takjn/GRRNble/GRRNble/allFonts.h

/*
 * allFonts.h font header for GLCD library 
 * The fonts listed below will be available in a sketch if this file is included
 *
 * If you create your own fonts you can add the header to this file
 *
 * Note that the build environment only holds a font in Flash if its selected 
 * so there is no penalty to including a font file here if its not used 
 */

#ifndef _allFonts_h_
#define _allFonts_h_

#ifdef __AVR__
#include <avr/pgmspace.h>
/** declare a font for AVR. */
#define GLCDFONTDECL(_n) static const uint8_t __attribute__ ((progmem))_n[]
#define readFontByte(addr) pgm_read_byte(addr)
#else  // __AVR__
/** declare a font. */
#define GLCDFONTDECL(_n) static const uint8_t _n[]
/** Fake read from flash. */
#define readFontByte(addr) (*(const unsigned char *)(addr))
#endif  // __AVR__
//------------------------------------------------------------------------------
// Font Indices
#define FONT_LENGTH			  0
#define FONT_FIXED_WIDTH	2
#define FONT_HEIGHT			  3
#define FONT_FIRST_CHAR		4
#define FONT_CHAR_COUNT		5
#define FONT_WIDTH_TABLE	6
//
// FONT_LENGTH is a 16 bit Big Endian length field.
// Unfortunately, FontCreator2 screwed up the value it put in the field
// so it is pretty much meaningless. However it still is used to indicate
// some special things.
// 00 00 (fixed width font with 1 padding pixel on right and below)
// 00 01 (fixed width font with no padding pixels)

// any other value means variable width font in FontCreator2 (thiele)
// format with pixel padding

//#include "Adafruit5x7.h"        // Font from Adafruit GFX library
//#include "font5x7.h"
//#include "lcd5x7.h"
//#include "Stang5x7.h"
//#include "X11fixed7x14.h"
//#include "X11fixed7x14B.h"
//#include "ZevvPeep8x16.h"
//
//#include "System5x7.h" 	        // system font (fixed width)
//#include "SystemFont5x7.h"      // backward compability System5x7 header
//#include "Iain5x7.h"		        // similar to system5x7 but proportional
//#include "Arial14.h"            // proportional font
//#include "Arial_bold_14.h"      // Bold proportional font
//#include "Corsiva_12.h"
//#include "Verdana_digits_24.h"  // large proportional font contains [0-9] and :
//
//#include "Callibri10.h"
//#include "Callibri11.h"
//#include "Callibri11_bold.h"
//#include "Callibri11_italic.h"
//#include "Callibri14.h"
//#include "Callibri15.h"
//#include "Cooper19.h"
//#include "Cooper21.h"
//#include "Cooper26.h"
//#include "TimesNewRoman13.h"
//#include "TimesNewRoman13_italic.h"
//#include "TimesNewRoman16.h"
//#include "TimesNewRoman16_bold.h"
//#include "TimesNewRoman16_italic.h"
//#include "Verdana12.h"
//#include "Verdana12_bold.h"
//#include "Verdana12_italic.h"
//#include "Roosewood22.h"
//#include "Roosewood26.h"
//
//#include "fixednums7x15.h"       // fixed width font - + , - . / [0-9] and :
//#include "fixednums8x16.h"       // fixed width font - + , - . / [0-9] and :
//#include "fixednums15x31.h"      // fixed width font - + , - . / [0-9] and :
//
//#include "CalBlk36.h"
//#include "CalLite24.h"
//#include "lcdnums12x16.h"	// font that looks like LCD digits
//#include "lcdnums14x24.h"	// font that looks like LCD digits
//#include "fixed_bold10x15.h"
//#include "Wendy3x5.h"
//#include "newbasic3x5.h"
//#include "TomThumbs3x6.h"
//
///*
// * These fonts require no-pad rendering code
// */
//#include "font8x8.h"		// fixed wider font but similar to system5x7 font
//#include "cp437font8x8.h"       // fixed Font from 80's IBM PC
//
///*
// * These fonts require UTF8 encoding support
// */
//
//#include "utf8font10x16.h"	// UTF8 font up to U+00FF
//				// http://www.fileformat.info/info/charset/UTF-8/list.htm

#include "BM_tube9x8.h"

#endif
